Leonezz/Anton/hardware/structure/PCStack/open_layer_3.SLDPRT

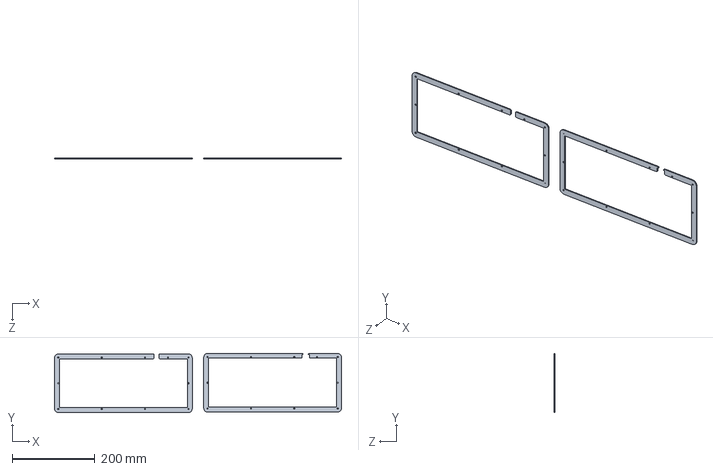
[picture p23: CAD file, 2021-10-28]
hardware/structure/PCStack/open_layer_3.SLDPRT
693.1 x 143.5 x 2.00 mm
