Leonezz/Anton/hardware/structure/PCStack/bottom_layer_3.SLDPRT

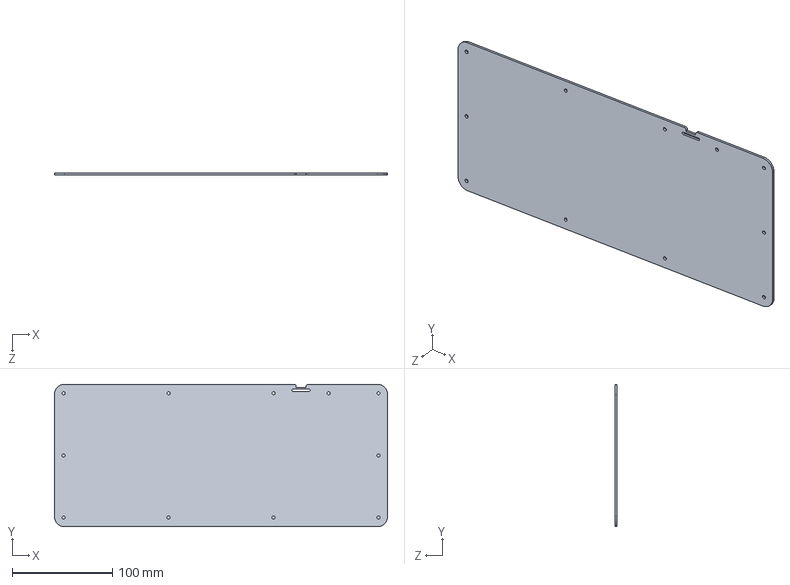
[picture p24: CAD file, 2021-10-28]
hardware/structure/PCStack/bottom_layer_3.SLDPRT
332.9 x 142.4 x 2.00 mm
