Leonezz/Anton/hardware/structure/PCStack/switch_layer_none.dxf

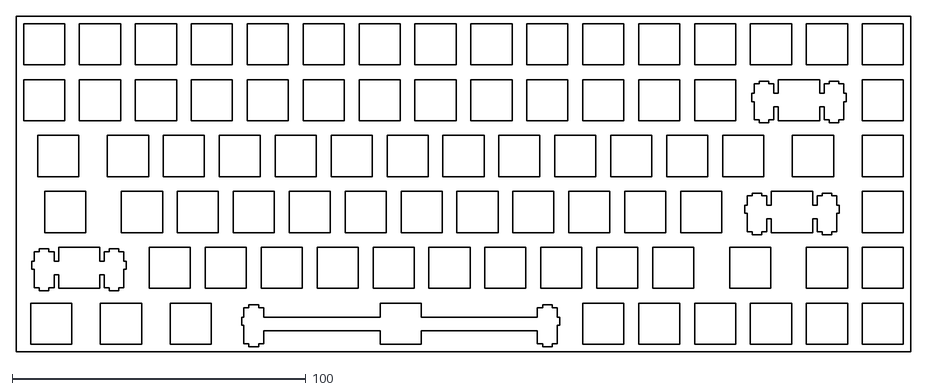
[picture p25: CAD file, 2021-10-28]
hardware/structure/PCStack/switch_layer_none.dxf
304.8 x 114.3
