Leonezz/Anton/hardware/structure/shell/imgs/assembly.png

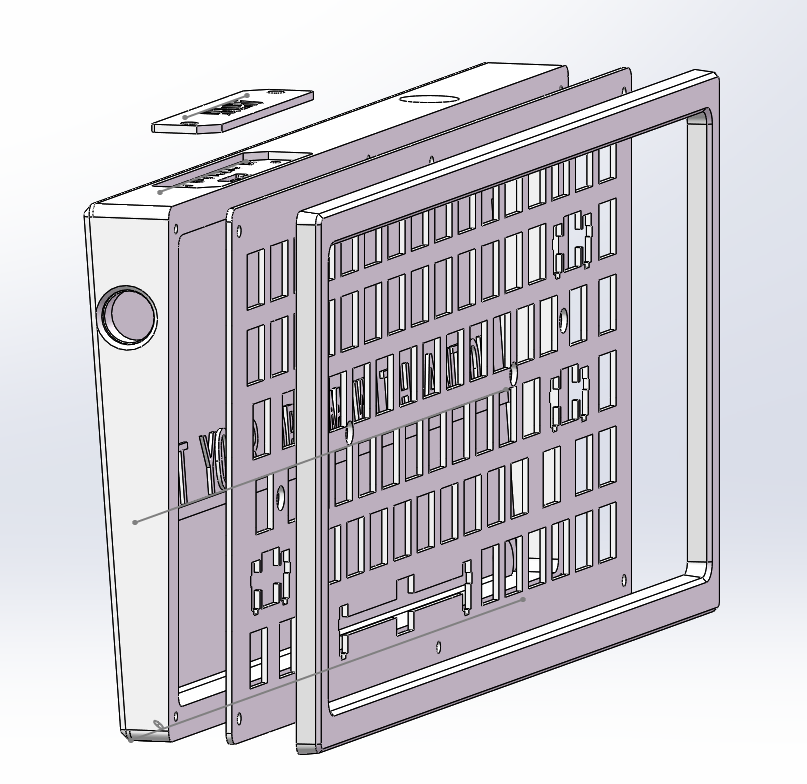
hardware/structure/shell/imgs/assembly.png
